TheRo0T/CAN-USB-STM32/STM32F105/SW4STM32/STM32F105 Configuration/Application/User/canhacker.h

#ifndef _CANHACKER_H
#define _CANHACKER_H

#include <stdint.h>
#include "stm32f1xx_hal.h"

#define CANHACKER_CMD_MAX_LENGTH 26

#define CANHACKER_HW_VER        0x10      // hardware version
#define CANHACKER_SW_VER        0x10      // software version
#define CANHACKER_SW_VER_MAJOR  0x01    // software major version
#define CANHACKER_SW_VER_MINOR  0x07    // software minor version
#define CANHACKER_SERIAL        "0001"    // device serial number
#define CANHACKER_CR 13
#define CANHACKER_ERROR 7
#define CANHACKER_SET_BITRATE     'S' // set CAN bit rate
#define CANHACKER_SET_BTR         's' // set CAN bit rate via
#define CANHACKER_OPEN_CAN_CHAN   'O' // open CAN channel
#define CANHACKER_CLOSE_CAN_CHAN  'C' // close CAN channel
#define CANHACKER_SEND_11BIT_ID   't' // send CAN message with 11bit ID
#define CANHACKER_SEND_29BIT_ID   'T' // send CAN message with 29bit ID
#define CANHACKER_SEND_R11BIT_ID  'r' // send CAN remote message with 11bit ID
#define CANHACKER_SEND_R29BIT_ID  'R' // send CAN remote message with 29bit ID
#define CANHACKER_READ_STATUS     'F' // read status flag byte
#define CANHACKER_SET_ACR         'M' // set Acceptance Code Register
#define CANHACKER_SET_AMR         'm' // set Acceptance Mask Register
#define CANHACKER_GET_VERSION     'V' // get hardware and software version
#define CANHACKER_GET_SW_VERSION  'v' // get software version only
#define CANHACKER_GET_SERIAL      'N' // get device serial number
#define CANHACKER_TIME_STAMP      'Z' // toggle time stamp setting
#define CANHACKER_READ_ECR        'E' // read Error Capture Register
#define CANHACKER_READ_ALCR       'A' // read Arbritation Lost Capture Register
#define CANHACKER_READ_REG        'G'   // read register conten from SJA1000
#define CANHACKER_WRITE_REG       'W'   // write register content to SJA1000
#define CANHACKER_LISTEN_ONLY     'L' // switch to listen only mode

#define TIME_STAMP_TICK 1000    // microseconds

typedef enum
{
    CANHACKER_TIMESTAMP_DISABLED = 0x00,
    CANHACKER_TIMESTAMP_ENABLED  = 0x01,

} CanHacker_TimestampTypeDef;

typedef struct
{
    CanHacker_TimestampTypeDef timestamp;
} CanHacker_HandleTypeDef;

void CanHacker_Init(CanHacker_HandleTypeDef *canhacker);
void CanHacker_Receive_Cmd(CanHacker_HandleTypeDef *canhacker, uint8_t *cmd_buf);
void CanHacker_Receive_CanMsg(CanHacker_HandleTypeDef *canhacker, CanRxMsgTypeDef *msg);
void CanHacker_ErrorCallback(CanHacker_HandleTypeDef *canhacker, char *message);
void CanHacker_CanTxMsgReadyCallback(CanHacker_HandleTypeDef *canhacker, CanTxMsgTypeDef *txMsg);
void CanHacker_UartMsgReadyCallback(CanHacker_HandleTypeDef *canhacker, uint8_t *line);
uint32_t CanHacker_GetTimestampCallback(CanHacker_HandleTypeDef *canhacker);
void CanHacker_StartTimerCallback(CanHacker_HandleTypeDef *canhacker);
void CanHacker_StopTimerCallback(CanHacker_HandleTypeDef *canhacker);

#endif
